era2-d2/ERA2-D2/Projeto/dados_monitoramento/ponto_3/Ponto 3.0.png

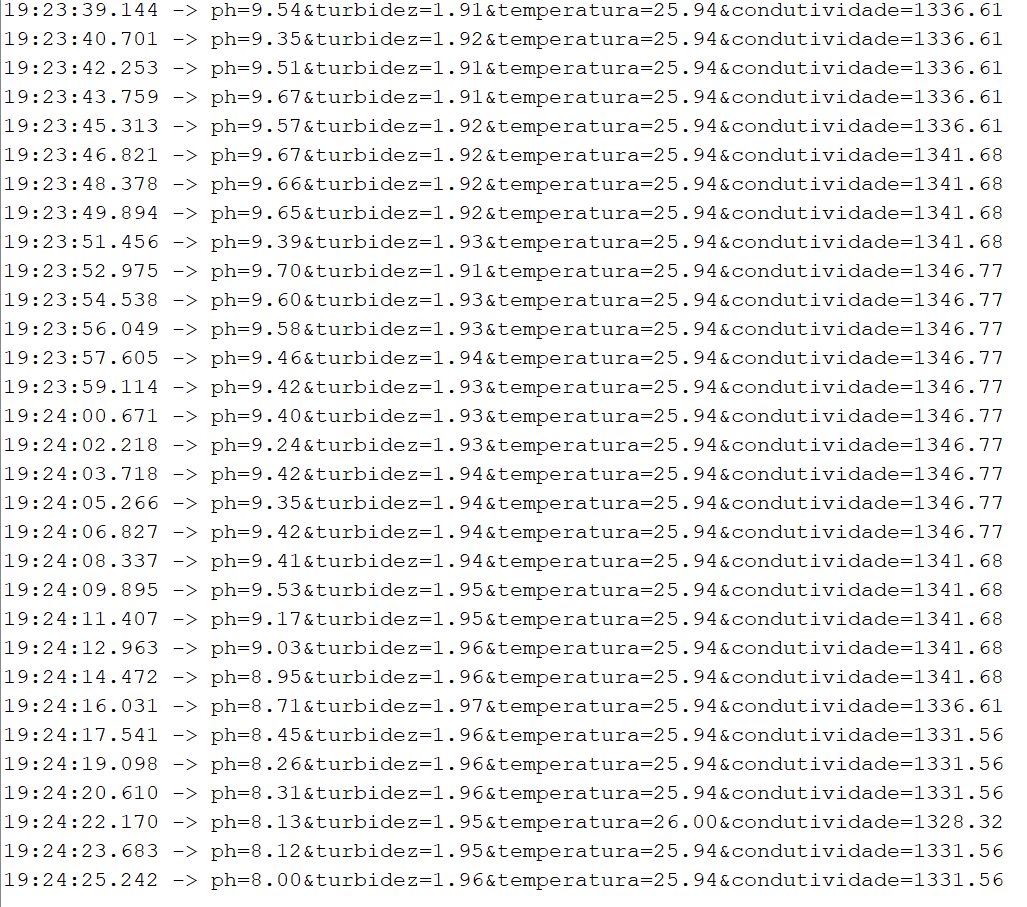
Projeto/dados_monitoramento/ponto_3/Ponto 3.0.png
