era2-d2/ERA2-D2/Projeto/imagens/direita.jpeg

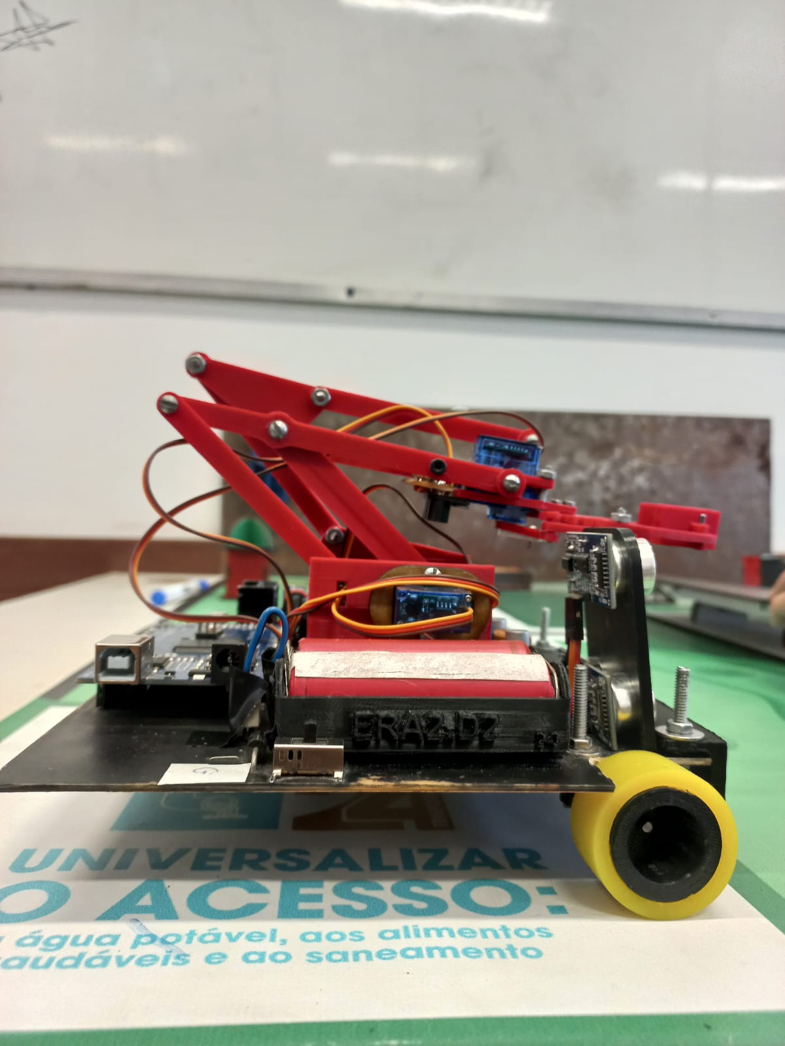
Projeto/imagens/direita.jpeg
