era2-d2/ERA2-D2/Projeto/imagens/pista1.jpeg

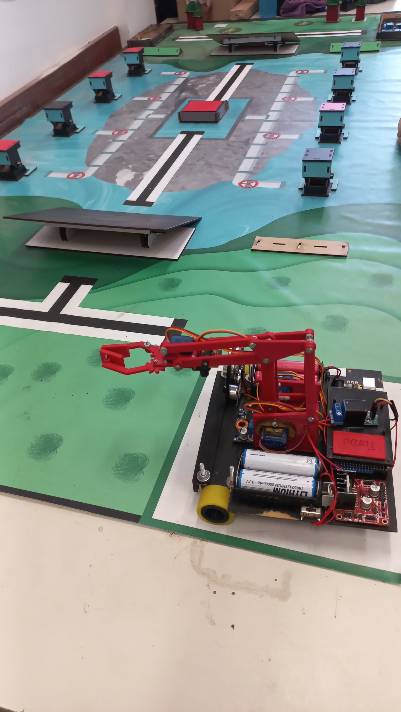
Projeto/imagens/pista1.jpeg
