era2-d2/ERA2-D2/Projeto/hardware/3d_prints/robo/Impressões Diversas/Cola_LDR.stl

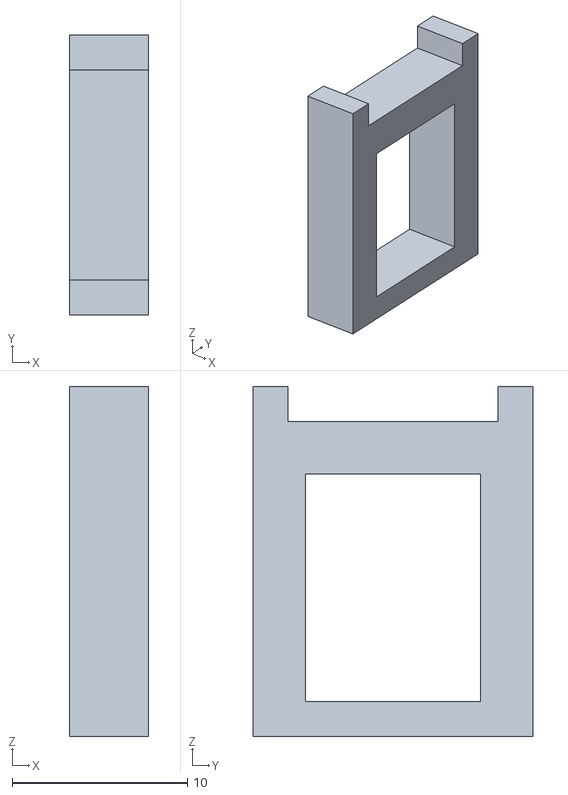
[picture p23: CAD file, 2025-05-30]
Projeto/hardware/3d_prints/robo/Impressões Diversas/Cola_LDR.stl
4.50 x 16.0 x 20.0
