era2-d2/ERA2-D2/Projeto/hardware/3d_prints/robo/Braço Robótico Versão 1/Base_Garra.stl

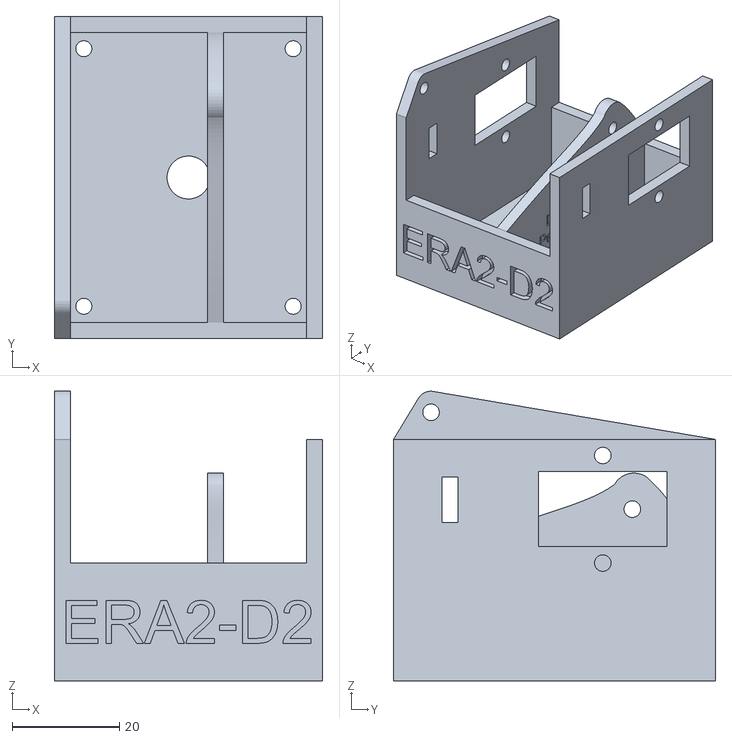
[picture p24: CAD file, 2025-05-30]
Projeto/hardware/3d_prints/robo/Braço Robótico Versão 1/Base_Garra.stl
50.0 x 60.0 x 54.0
