era2-d2/ERA2-D2/Projeto/hardware/3d_prints/robo/Impressões Diversas/SKYWALKER_2.0.stl

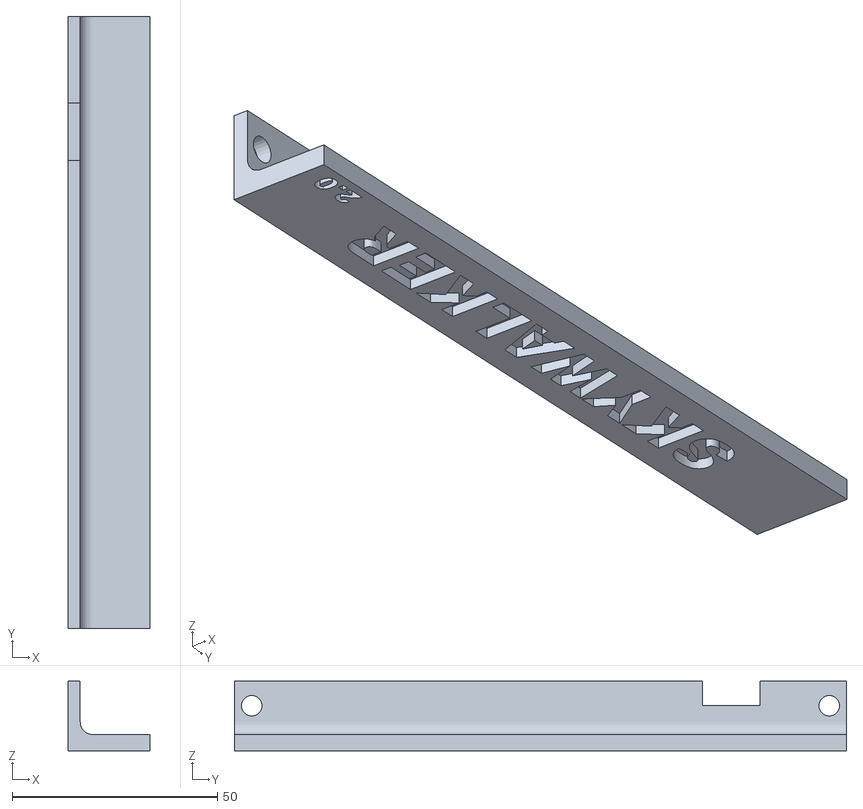
[picture p25: CAD file, 2025-05-30]
Projeto/hardware/3d_prints/robo/Impressões Diversas/SKYWALKER_2.0.stl
20.0 x 149.0 x 17.0
