era2-d2/ERA2-D2/Projeto/hardware/3d_prints/robo/Braço Robótico Versão 1/Garra.stl

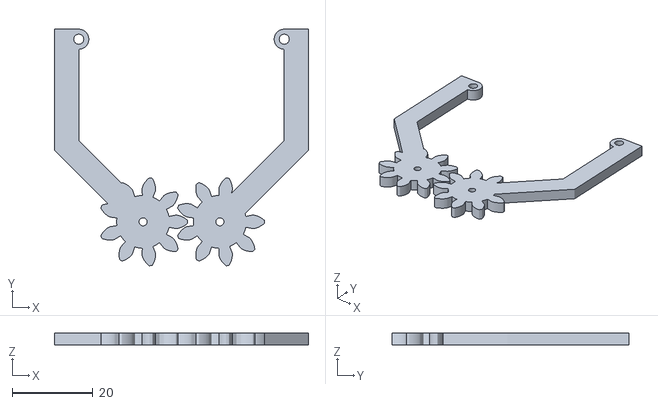
[picture p26: CAD file, 2025-05-30]
Projeto/hardware/3d_prints/robo/Braço Robótico Versão 1/Garra.stl
62.8 x 58.6 x 3.00
