era2-d2/ERA2-D2/Projeto/hardware/3d_prints/robo/Impressões Diversas/PINO.stl

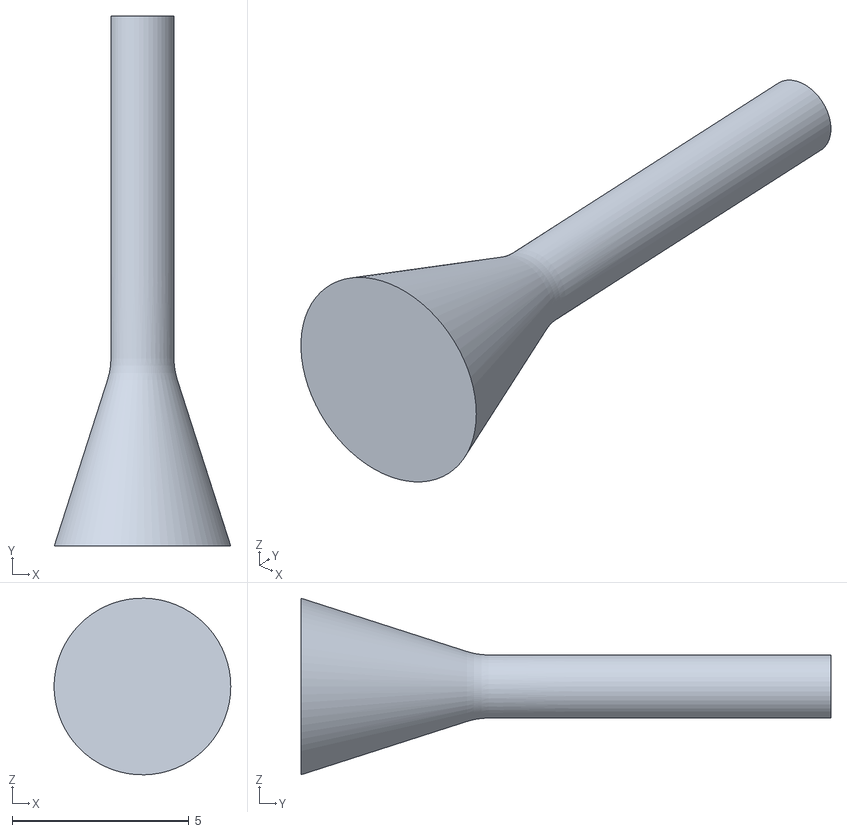
[picture p27: CAD file, 2025-05-30]
Projeto/hardware/3d_prints/robo/Impressões Diversas/PINO.stl
5.00 x 15.0 x 5.00
