era2-d2/ERA2-D2/Projeto/hardware/3d_prints/robo/Braço Robótico Versão 1/Ponta_Garra.stl

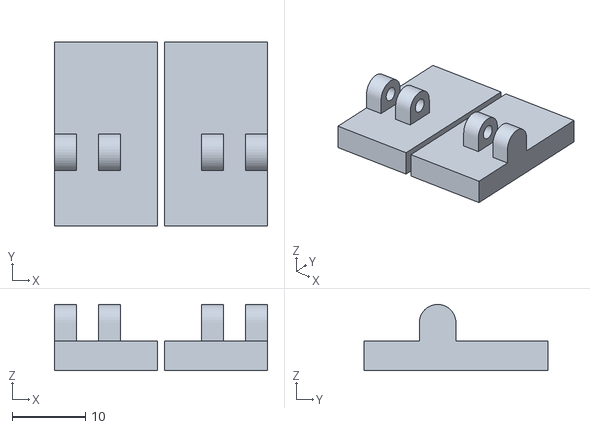
[picture p28: CAD file, 2025-05-30]
Projeto/hardware/3d_prints/robo/Braço Robótico Versão 1/Ponta_Garra.stl
29.0 x 25.0 x 9.00
