era2-d2/ERA2-D2/Projeto/hardware/3d_prints/robo/Impressões Diversas/Bolinha_v3.stl

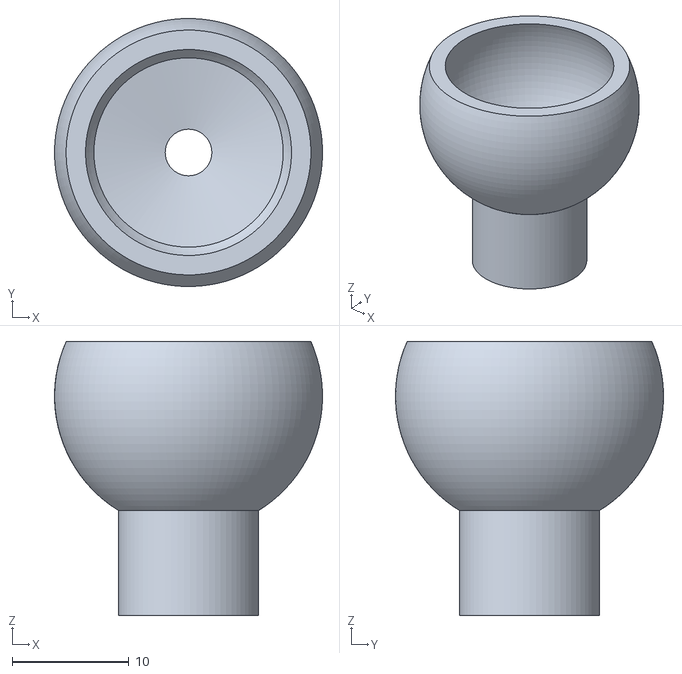
[picture p29: CAD file, 2025-05-30]
Projeto/hardware/3d_prints/robo/Impressões Diversas/Bolinha_v3.stl
23.0 x 23.0 x 23.5
