era2-d2/ERA2-D2/Projeto/hardware/3d_prints/robo/Braço Robótico Versão 1/Suporte_Servomotor_Garra.stl

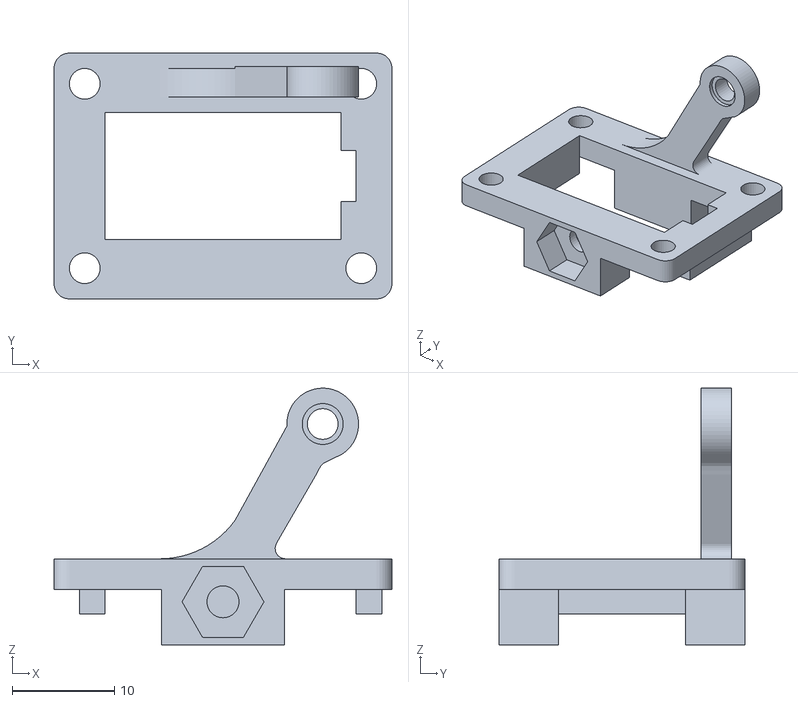
[picture p30: CAD file, 2025-05-30]
Projeto/hardware/3d_prints/robo/Braço Robótico Versão 1/Suporte_Servomotor_Garra.stl
33.0 x 24.0 x 25.1
