era2-d2/ERA2-D2/Projeto/hardware/3d_prints/robo/Impressões Diversas/Suporte_Bateria.stl

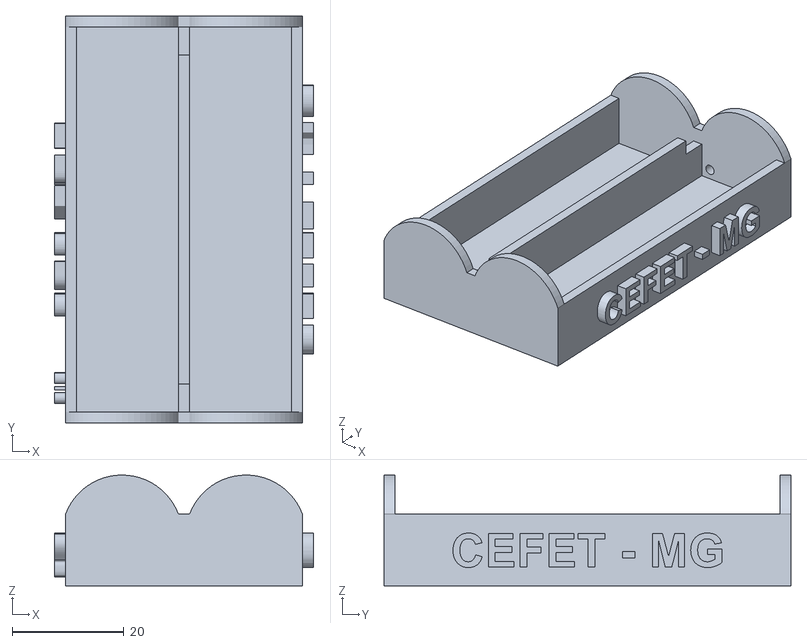
[picture p31: CAD file, 2025-05-30]
Projeto/hardware/3d_prints/robo/Impressões Diversas/Suporte_Bateria.stl
46.5 x 73.0 x 19.9
