era2-d2/ERA2-D2/Projeto/hardware/3d_prints/robo/Braço Robótico Versão 1/Mecanização_Braço.stl

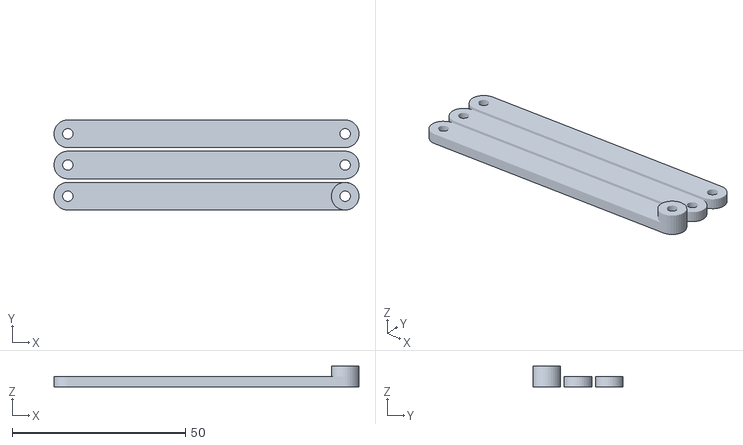
[picture p32: CAD file, 2025-05-30]
Projeto/hardware/3d_prints/robo/Braço Robótico Versão 1/Mecanização_Braço.stl
88.0 x 26.0 x 6.00
