era2-d2/ERA2-D2/Projeto/hardware/3d_prints/robo/Impressões Diversas/Base_Ultrassônico.stl

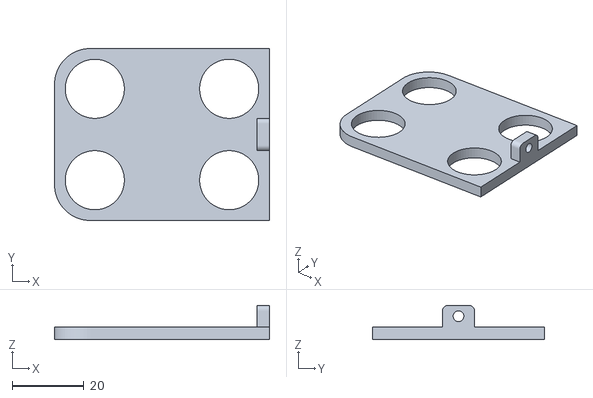
[picture p33: CAD file, 2025-05-30]
Projeto/hardware/3d_prints/robo/Impressões Diversas/Base_Ultrassônico.stl
60.0 x 48.0 x 9.50
